sssata/BluetoothSpeaker/CAD3/Samsung INR18650-29R.SLDPRT

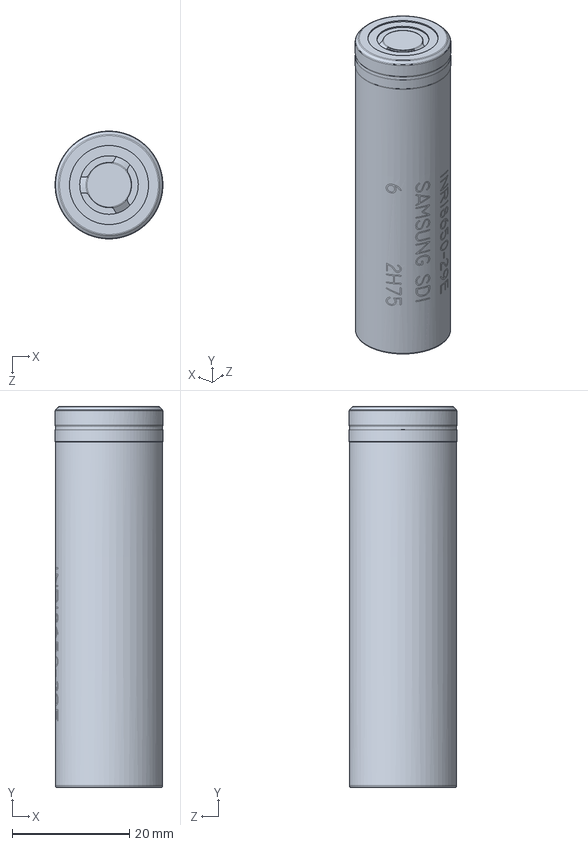
[picture p21: CAD file, 2020-11-30]
CAD3/Samsung INR18650-29R.SLDPRT
18.4 x 64.9 x 18.4 mm
