sssata/BluetoothSpeaker/CAD/020 USBC port.SLDPRT

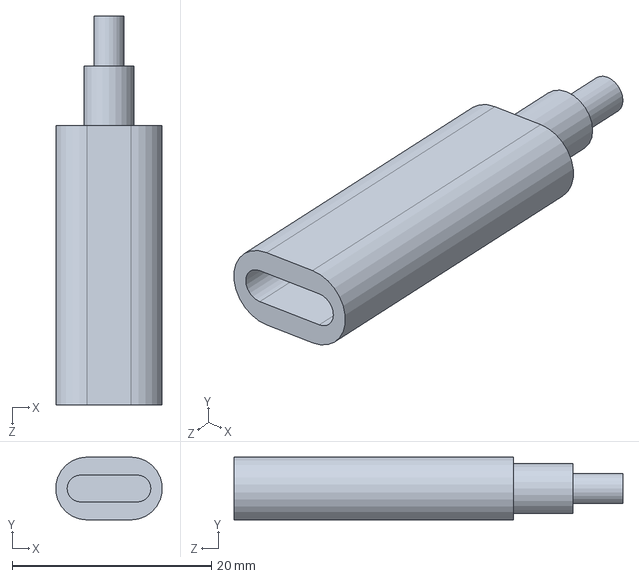
[picture p22: CAD file, 2020-11-30]
CAD/020 USBC port.SLDPRT
10.7 x 6.30 x 39.0 mm
