sssata/BluetoothSpeaker/CAD/003 reflector.SLDPRT

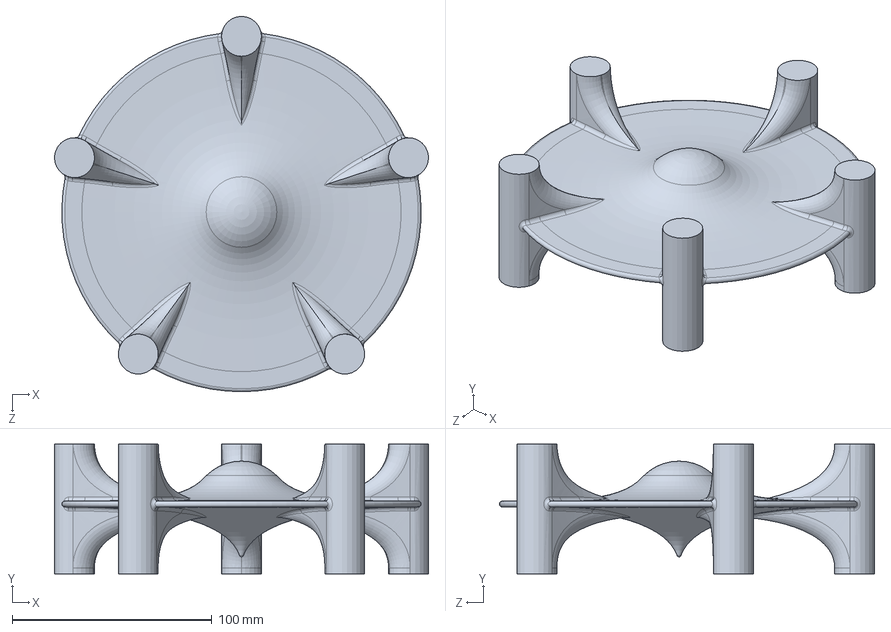
[picture p23: CAD file, 2020-11-30]
CAD/003 reflector.SLDPRT
187.4 x 65.0 x 188.0 mm
