sssata/BluetoothSpeaker/CAD/401 Dayton Audio DC28F-8 tweeter.SLDPRT

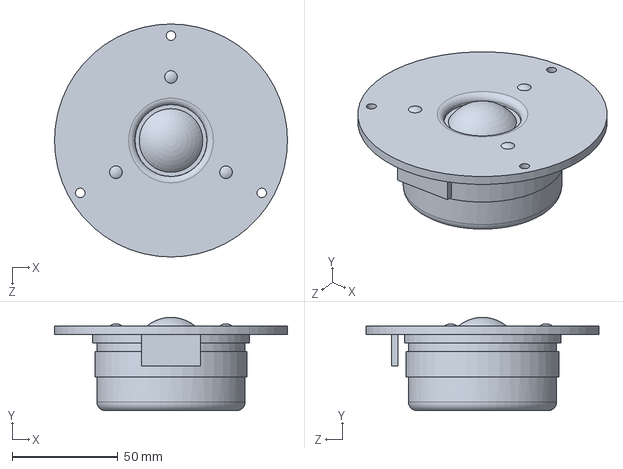
[picture p24: CAD file, 2020-11-30]
CAD/401 Dayton Audio DC28F-8 tweeter.SLDPRT
110.0 x 44.1 x 110.0 mm
