sssata/BluetoothSpeaker/CAD3/156 base pad.SLDPRT

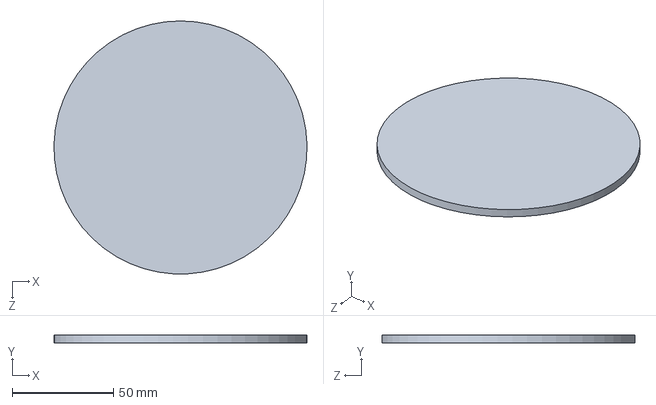
[picture p25: CAD file, 2020-11-30]
CAD3/156 base pad.SLDPRT
124.9 x 4.00 x 125.0 mm
