sssata/BluetoothSpeaker/CAD3/006 bluetooth button.SLDPRT

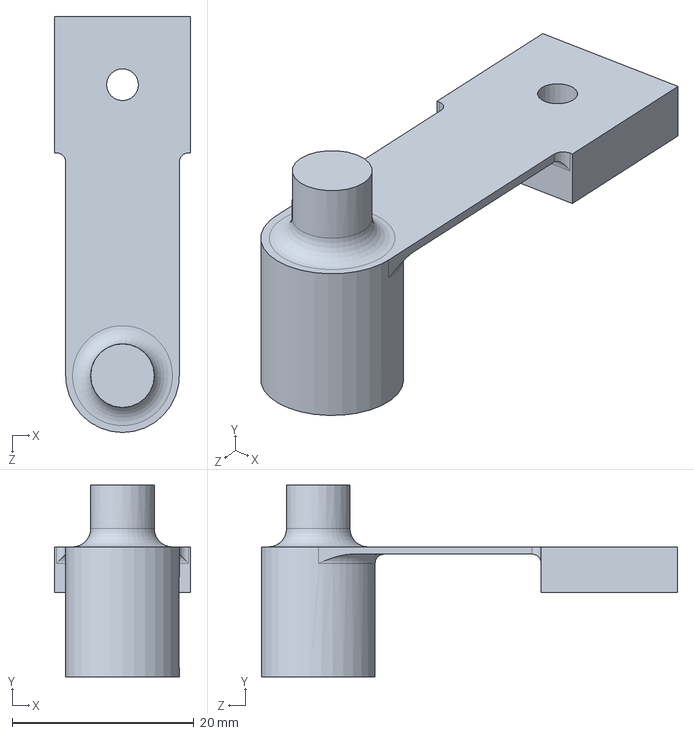
[picture p26: CAD file, 2020-11-30]
CAD3/006 bluetooth button.SLDPRT
15.0 x 21.1 x 45.8 mm
