sssata/BluetoothSpeaker/CAD3/152 U8M Switch.SLDPRT

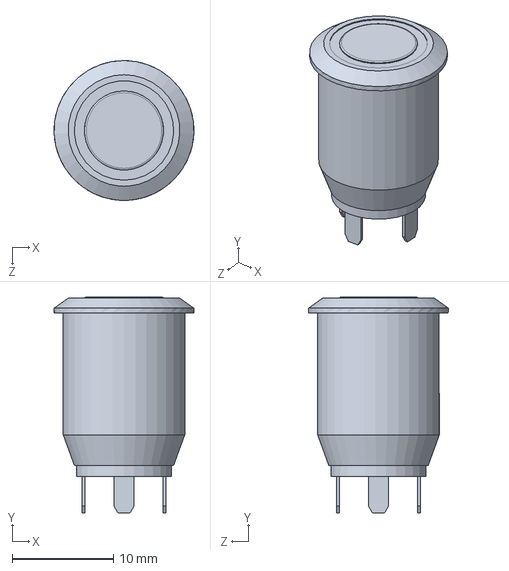
[picture p27: CAD file, 2020-11-30]
CAD3/152 U8M Switch.SLDPRT
13.8 x 21.3 x 13.8 mm
