sssata/BluetoothSpeaker/CAD/400 Dayton Audio 105-PR 4inch.SLDPRT

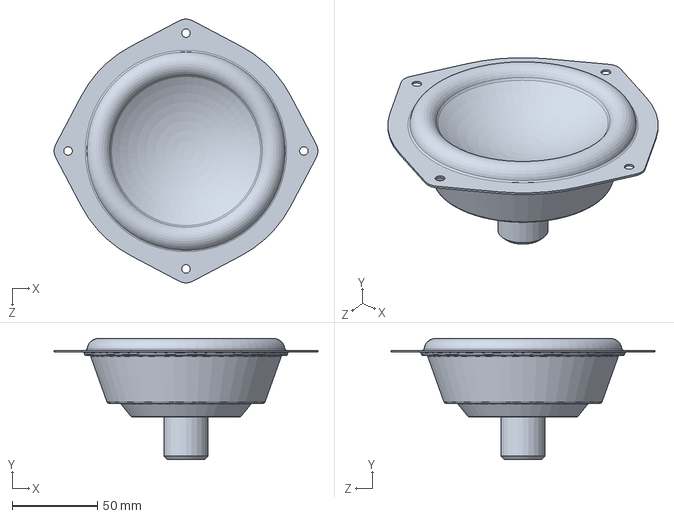
[picture p28: CAD file, 2020-11-30]
CAD/400 Dayton Audio 105-PR 4inch.SLDPRT
154.5 x 71.0 x 154.5 mm
