sssata/BluetoothSpeaker/CAD3/113 M3x25 SHCS.SLDPRT

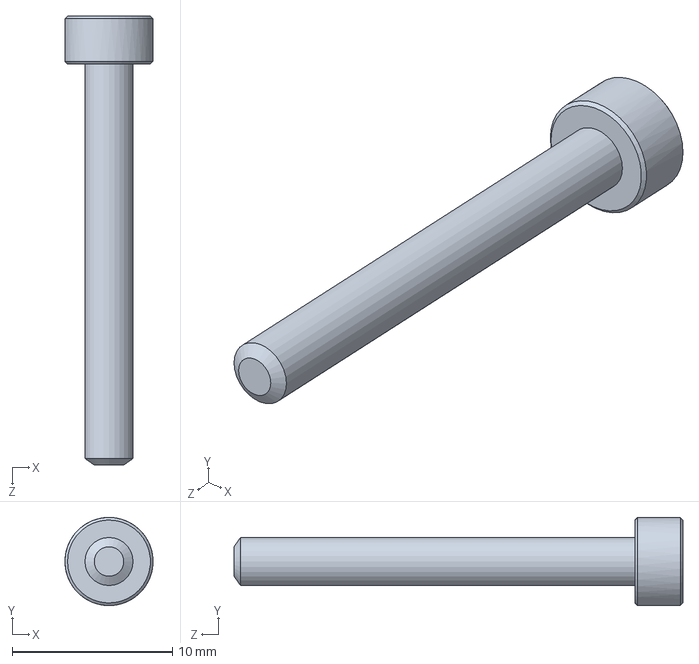
[picture p29: CAD file, 2020-11-30]
CAD3/113 M3x25 SHCS.SLDPRT
5.50 x 5.50 x 28.0 mm
