sssata/BluetoothSpeaker/CAD3/100 M3 Insert.SLDPRT

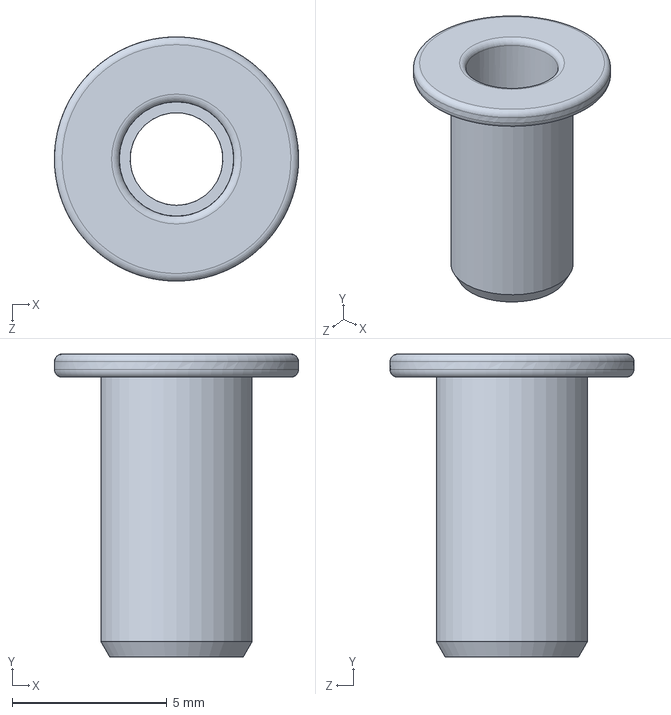
[picture p30: CAD file, 2020-11-30]
CAD3/100 M3 Insert.SLDPRT
7.90 x 9.80 x 7.90 mm
