sssata/BluetoothSpeaker/CAD3/154 5mm LED.SLDPRT

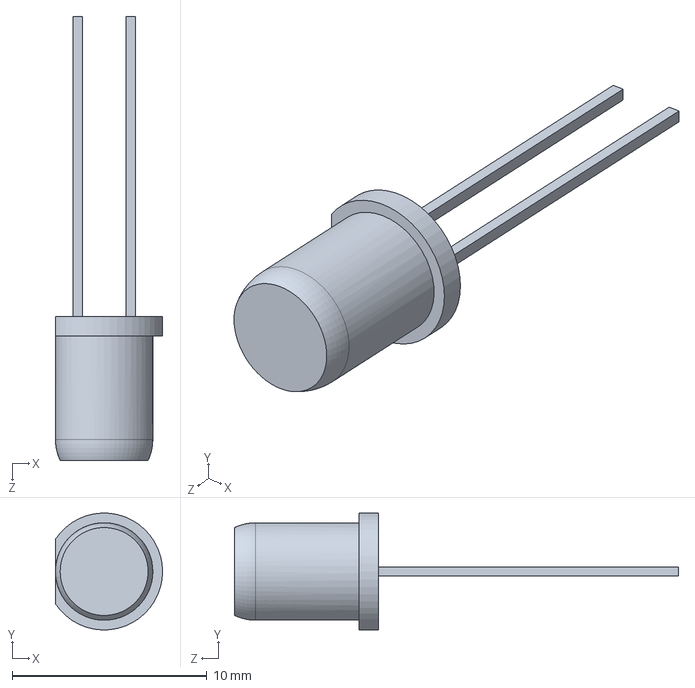
[picture p31: CAD file, 2020-11-30]
CAD3/154 5mm LED.SLDPRT
5.50 x 5.99 x 22.8 mm
