sssata/BluetoothSpeaker/CAD/301 Dayton Audio KAB-BE PCB.SLDPRT

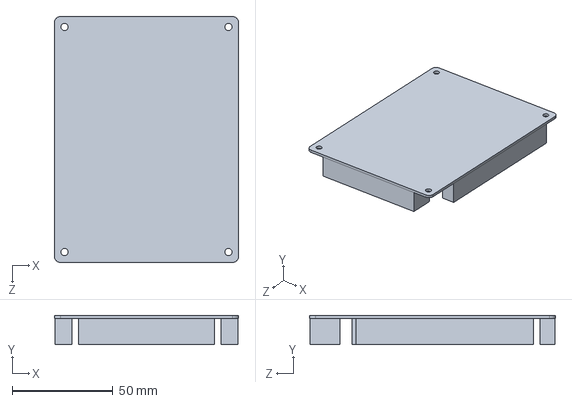
[picture p32: CAD file, 2020-11-30]
CAD/301 Dayton Audio KAB-BE PCB.SLDPRT
91.5 x 14.5 x 122.2 mm
