sssata/BluetoothSpeaker/CAD3/010 top woofer plate.SLDPRT

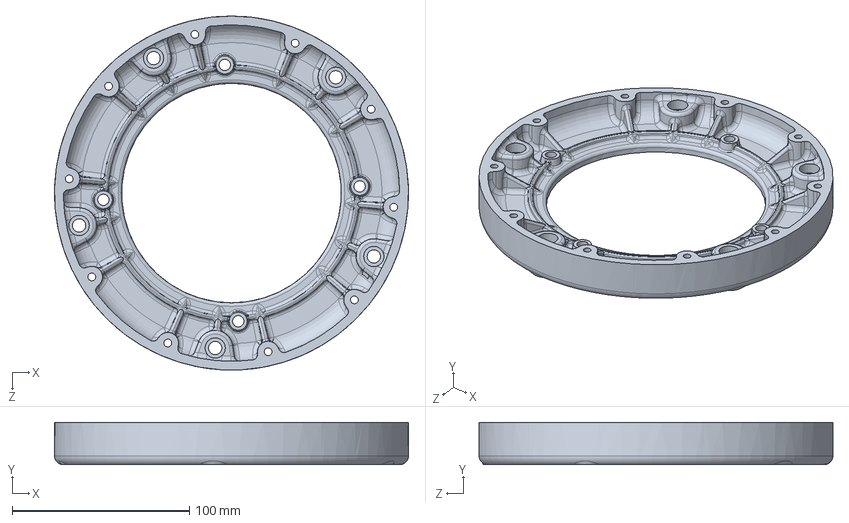
[picture p33: CAD file, 2020-11-30]
CAD3/010 top woofer plate.SLDPRT
200.0 x 24.0 x 199.9 mm
