sssata/BluetoothSpeaker/CAD3/112 M5x80 SHCS.SLDPRT

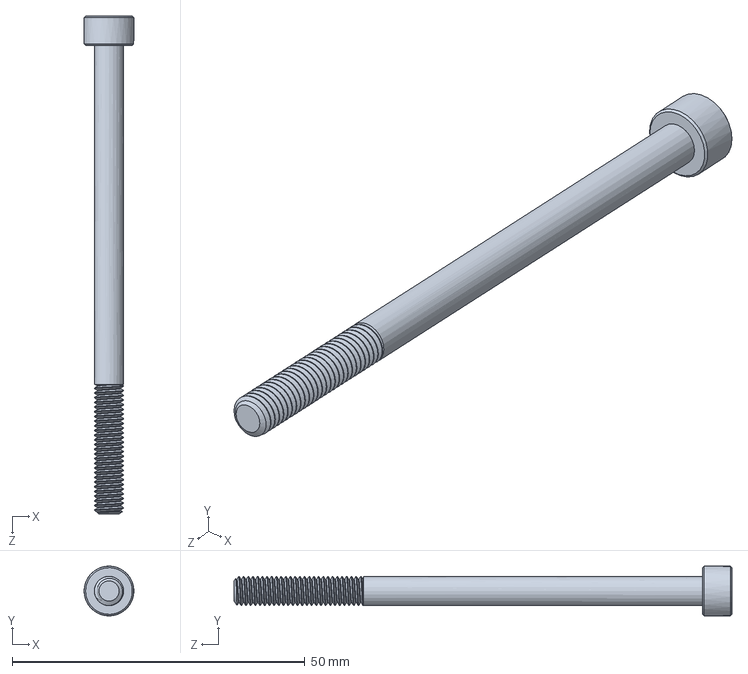
[picture p34: CAD file, 2020-11-30]
CAD3/112 M5x80 SHCS.SLDPRT
8.50 x 8.49 x 85.0 mm
