sssata/BluetoothSpeaker/CAD/153 Volume Knob.SLDPRT

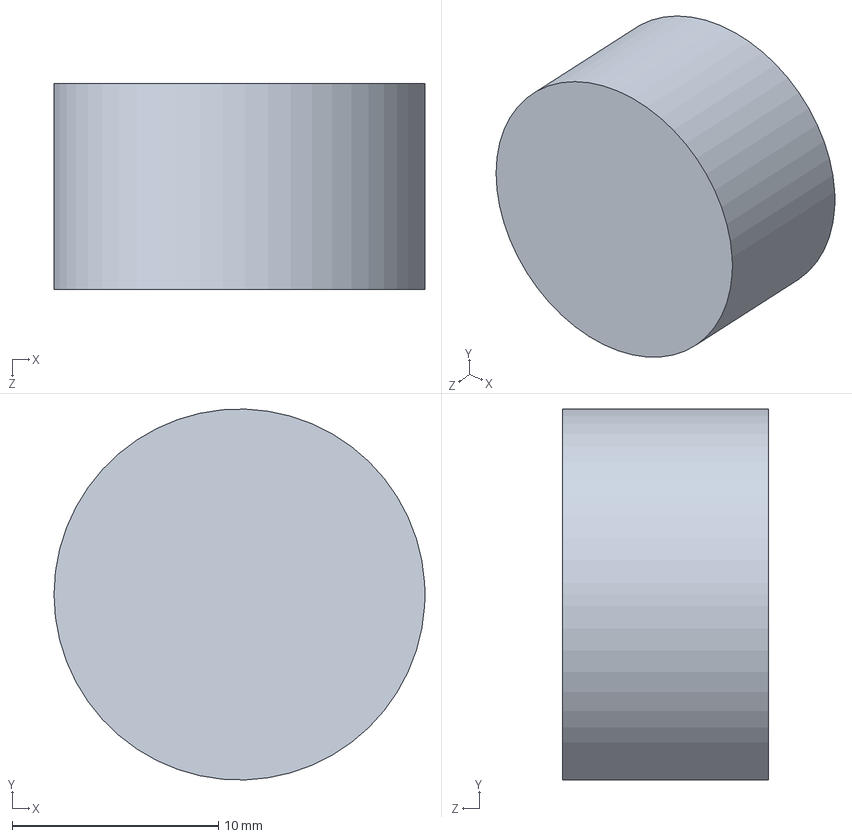
[picture p35: CAD file, 2020-11-30]
CAD/153 Volume Knob.SLDPRT
18.0 x 18.0 x 10.0 mm
