sssata/BluetoothSpeaker/CAD3/150 10K Pot.SLDPRT

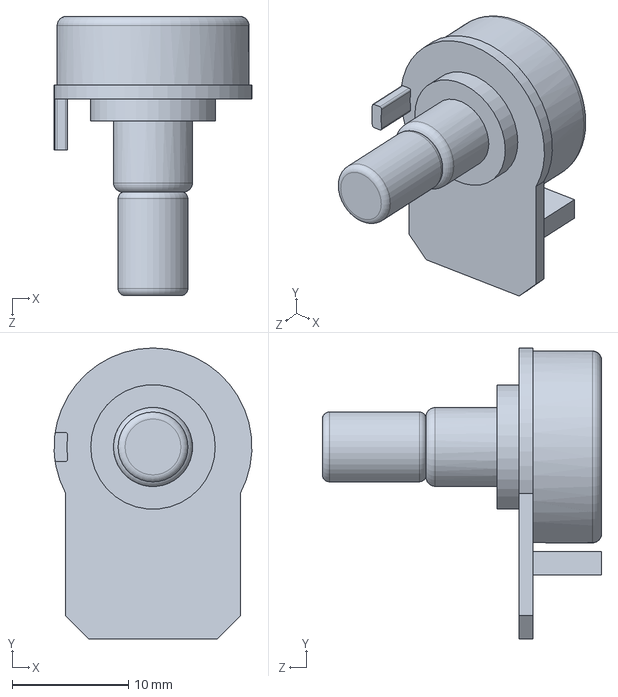
[picture p36: CAD file, 2020-11-30]
CAD3/150 10K Pot.SLDPRT
17.0 x 25.0 x 24.0 mm
