sssata/BluetoothSpeaker/CAD/300 Bluetooth board.SLDPRT

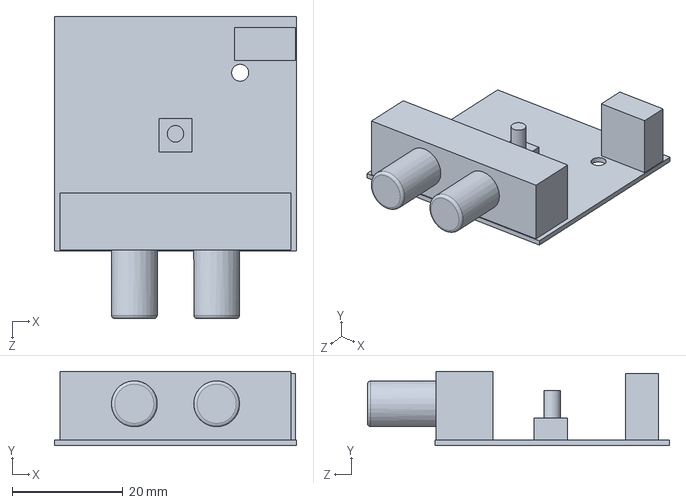
[picture p37: CAD file, 2020-11-30]
CAD/300 Bluetooth board.SLDPRT
43.8 x 13.4 x 54.7 mm
