sssata/BluetoothSpeaker/CAD/402 Tang Band W5-1138SMF.SLDPRT

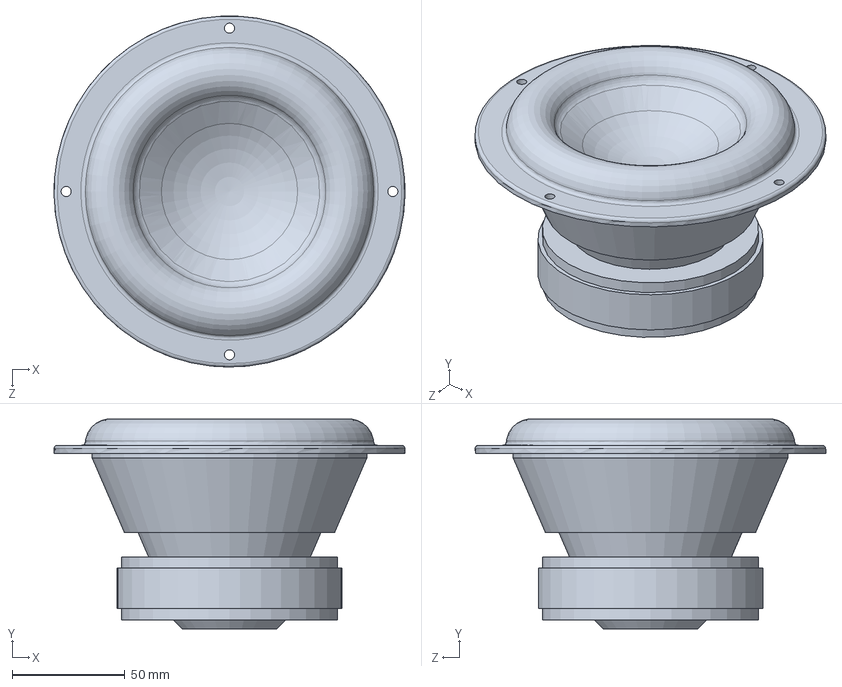
[picture p38: CAD file, 2020-11-30]
CAD/402 Tang Band W5-1138SMF.SLDPRT
155.7 x 93.1 x 155.8 mm
