sssata/BluetoothSpeaker/CAD/301 Dayton Audio DSPB-250 Amplifier Board.SLDPRT

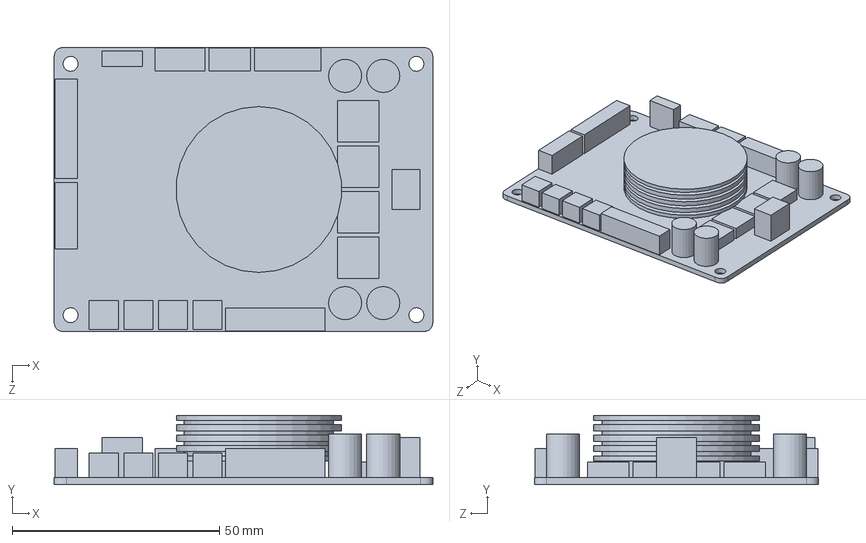
[picture p39: CAD file, 2020-11-30]
CAD/301 Dayton Audio DSPB-250 Amplifier Board.SLDPRT
91.4 x 16.7 x 68.6 mm
